abidanBrito/sensor-tech/src/mainProgram/ADC_API.h

/*  ------------------------------------------------------------------------
    AUTHOR:         Abidan Brito Clavijo
    FILE:           fileName.h
    DATE:           02/01/2020
    STATE:          DONE
    FUNCTIONALITY:  Add header guards to ADC library to avoid several
                    inclusions.
    ------------------------------------------------------------------------
    NOTICE: (C) Copyright 2019 by Abidan Brito Clavijo. All rights reserved.
    ------------------------------------------------------------------------ */
#ifndef ADC_API_H
#define ADC_API_H

#include <Adafruit_ADS1015.h>

#endif
